wvdv2002/SMA-SB2500-Off-Grid/code/solarinv_CubeMX.png

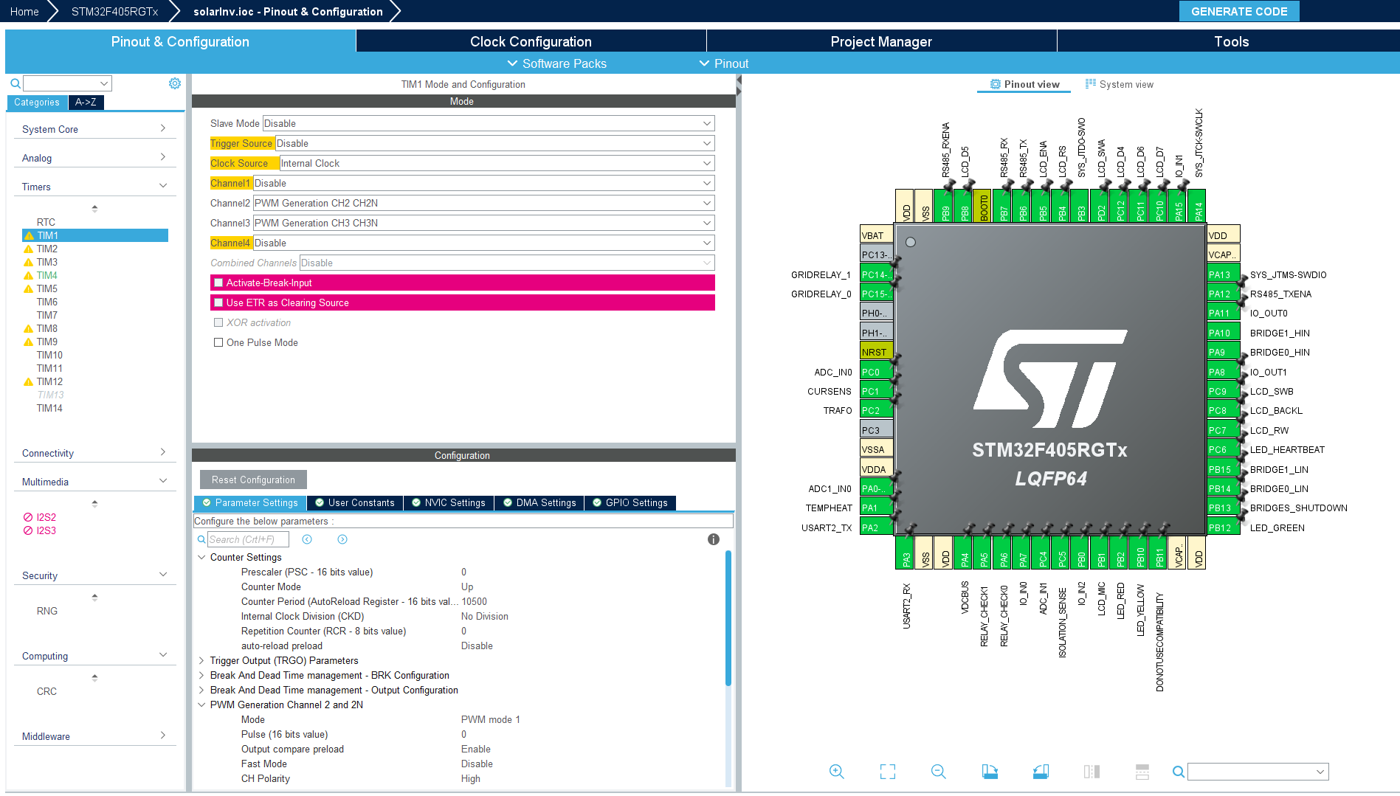
code/solarinv_CubeMX.png
