wvdv2002/SMA-SB2500-Off-Grid/images/2022-01-16 18.45.59.jpg

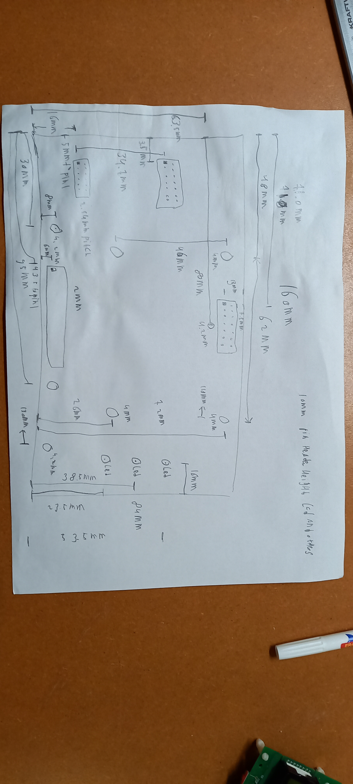
images/2022-01-16 18.45.59.jpg
