wvdv2002/SMA-SB2500-Off-Grid/images/commboardunderside.jpg

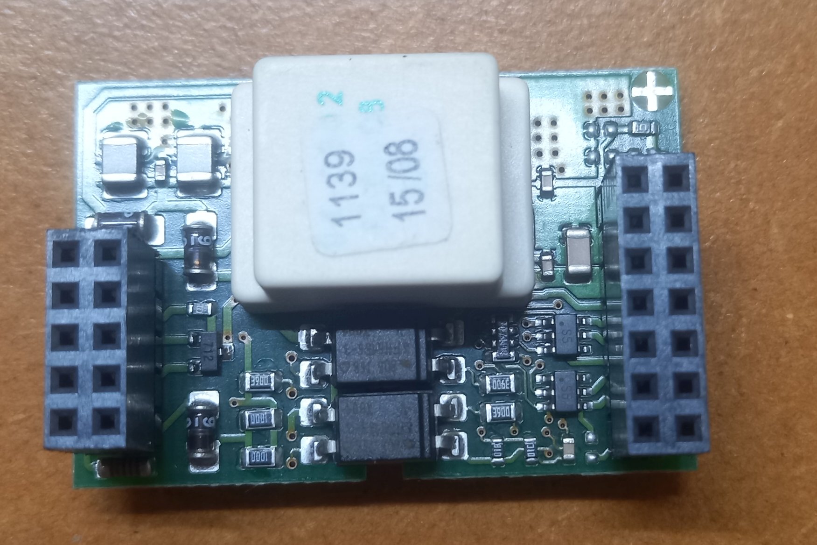
images/commboardunderside.jpg
