wvdv2002/SMA-SB2500-Off-Grid/images/DCBus.png

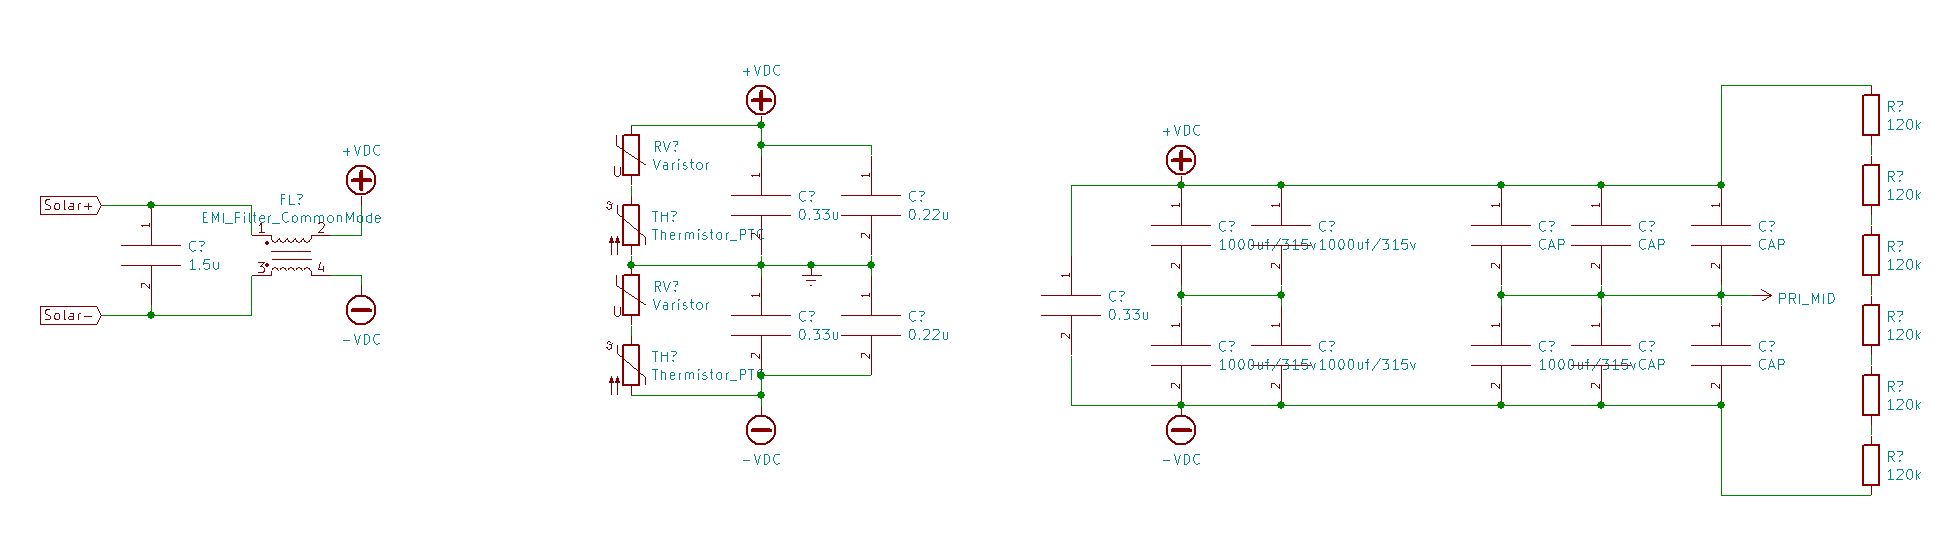
images/DCBus.png
