wvdv2002/SMA-SB2500-Off-Grid/images/EMCFilter.jpg

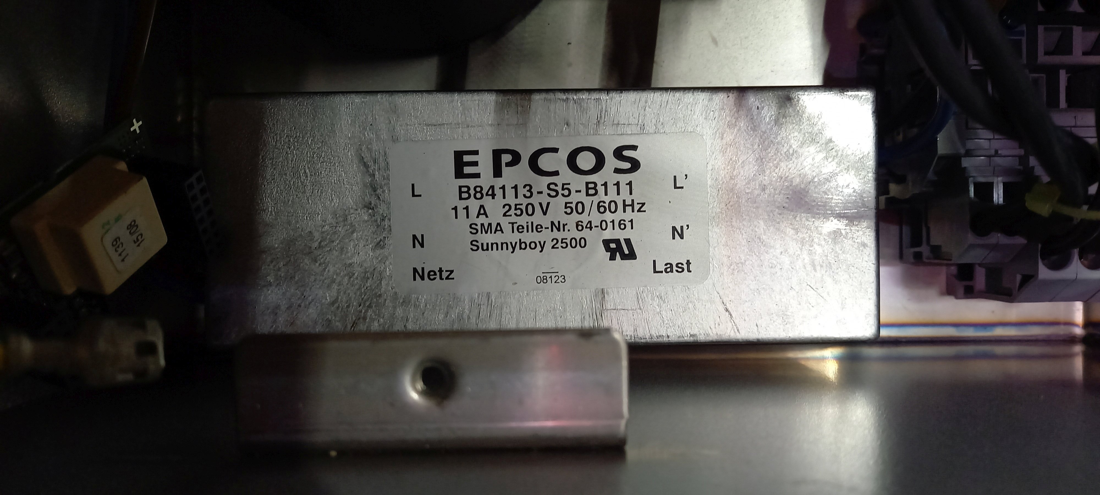
images/EMCFilter.jpg
