wvdv2002/SMA-SB2500-Off-Grid/images/inductor.jpg

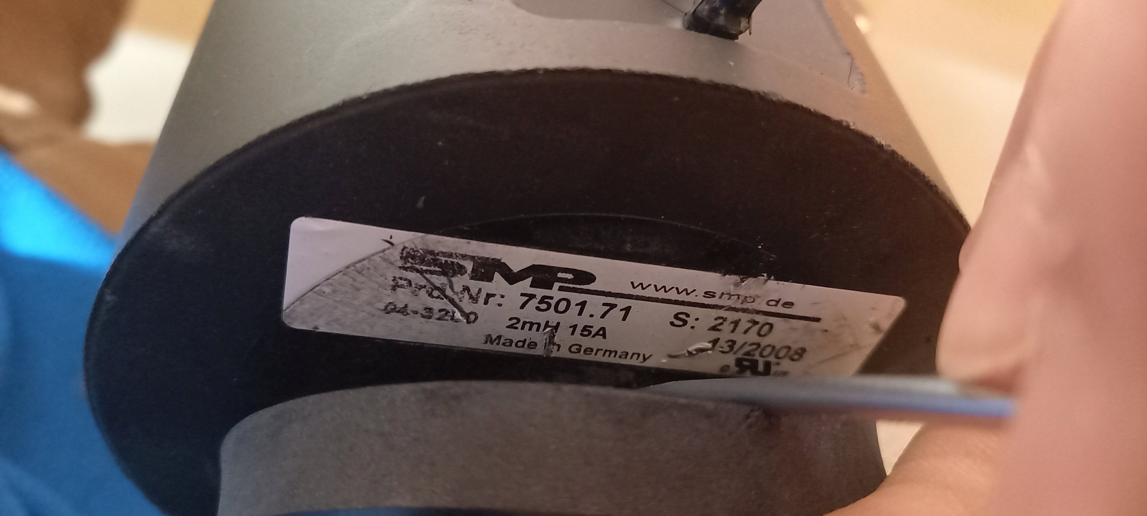
images/inductor.jpg
