wvdv2002/SMA-SB2500-Off-Grid/images/inverterInside.jpg

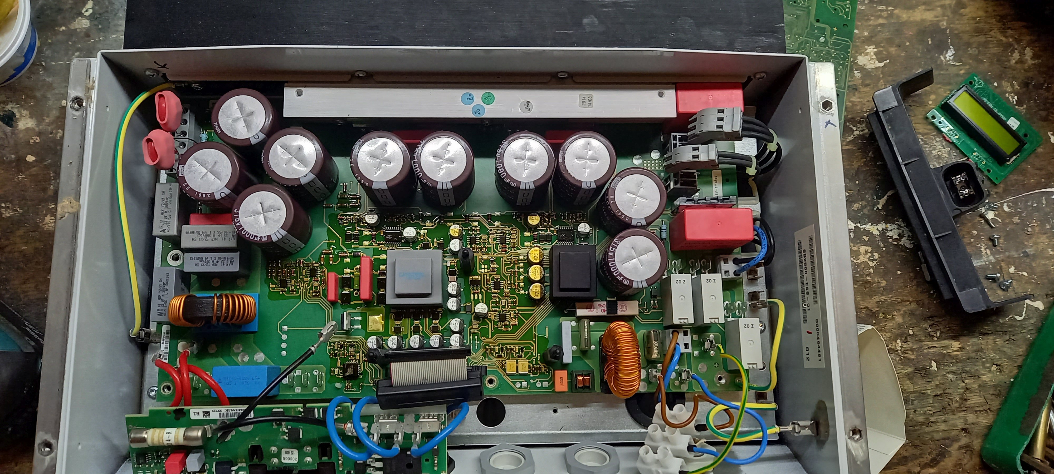
images/inverterInside.jpg
