wvdv2002/SMA-SB2500-Off-Grid/images/lcdon.jpg

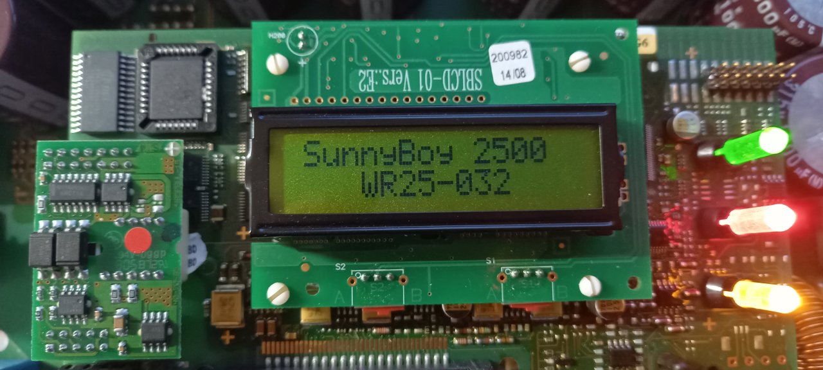
images/lcdon.jpg
