wvdv2002/SMA-SB2500-Off-Grid/images/logicboard2.jpg

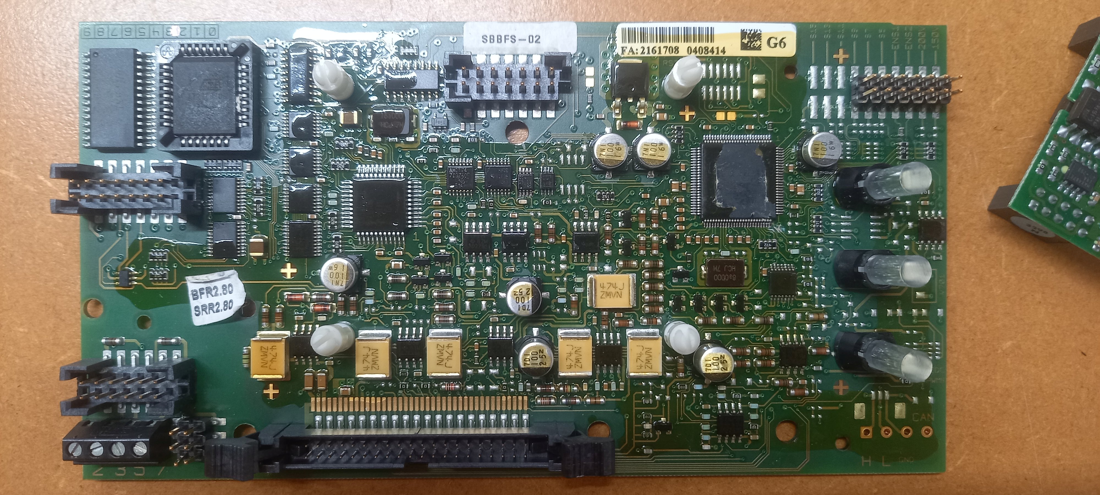
images/logicboard2.jpg
