wvdv2002/SMA-SB2500-Off-Grid/images/logicboard.jpg

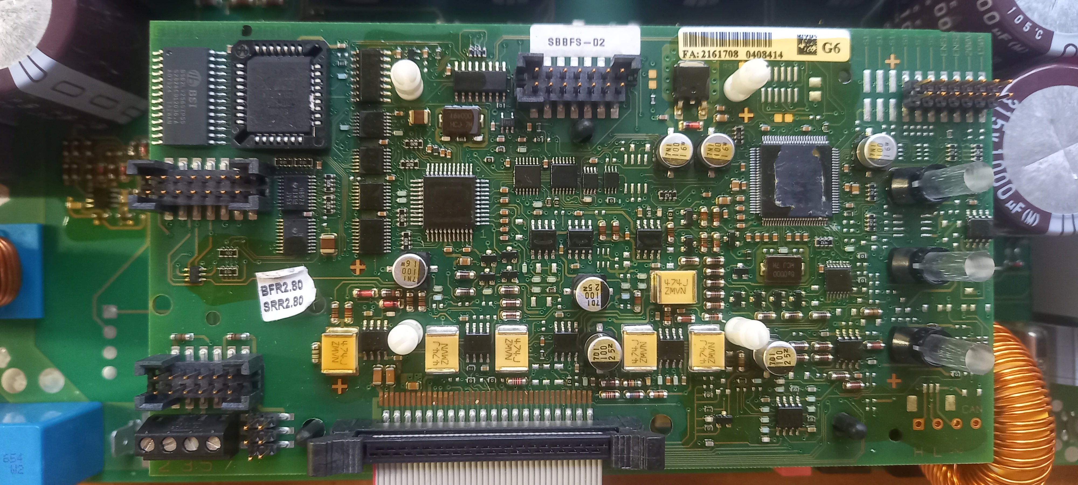
images/logicboard.jpg
