wvdv2002/SMA-SB2500-Off-Grid/images/logicboardcloseup.jpg

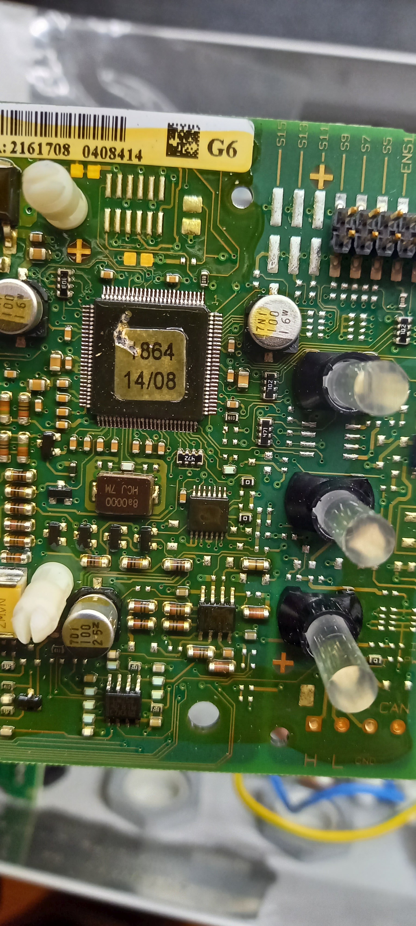
images/logicboardcloseup.jpg
