wvdv2002/SMA-SB2500-Off-Grid/images/logicboardcomplete.jpg

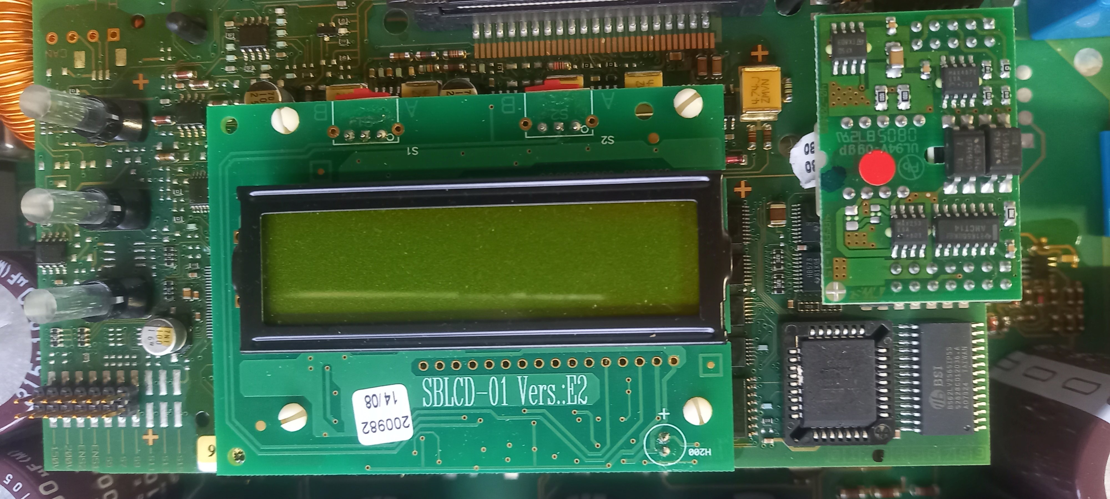
images/logicboardcomplete.jpg
