wvdv2002/SMA-SB2500-Off-Grid/images/LogicboardSizes.jpg

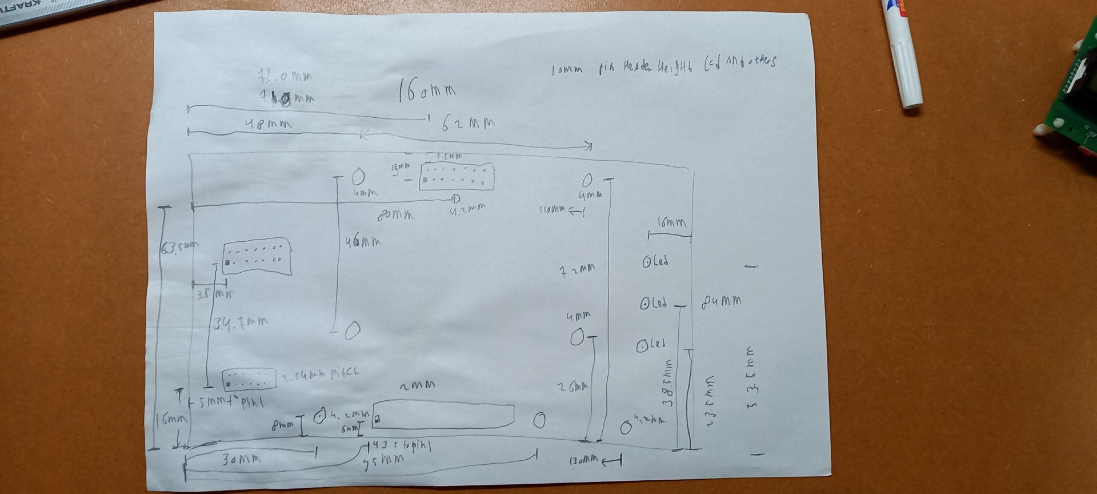
images/LogicboardSizes.jpg
