wvdv2002/SMA-SB2500-Off-Grid/images/logicboardunderside.jpg

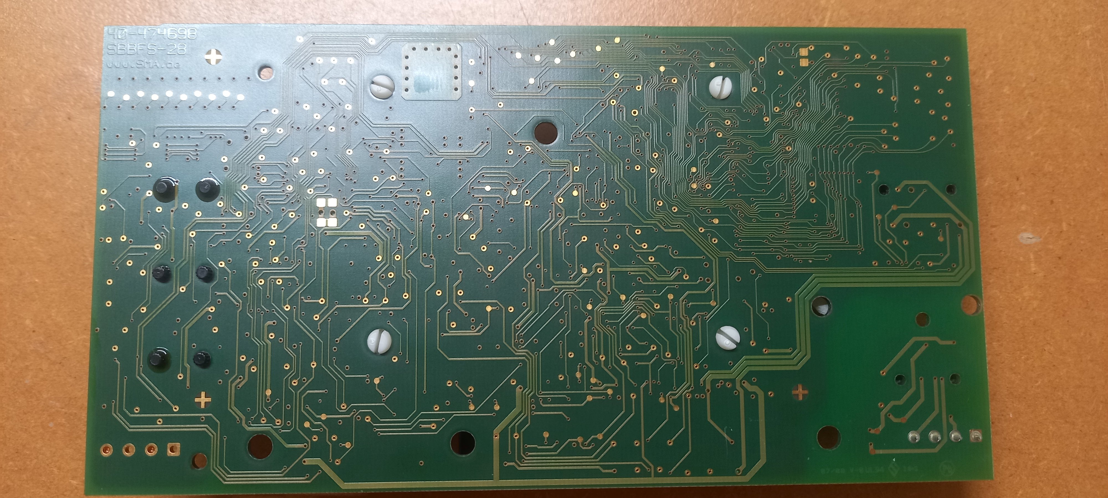
images/logicboardunderside.jpg
