wvdv2002/SMA-SB2500-Off-Grid/images/newController/controllerPCB.jpg

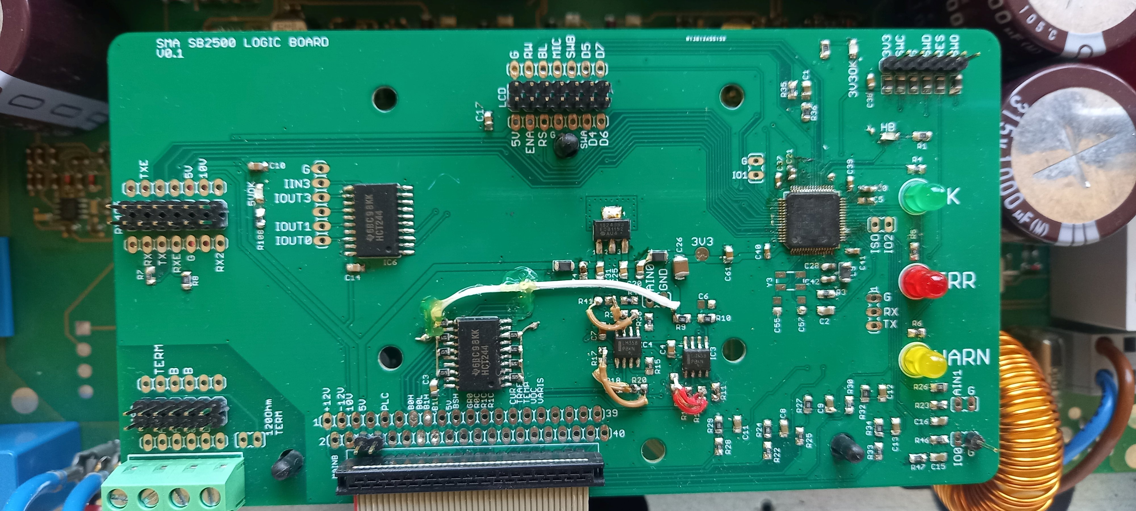
images/newController/controllerPCB.jpg
