wvdv2002/SMA-SB2500-Off-Grid/images/powerboard2.jpg

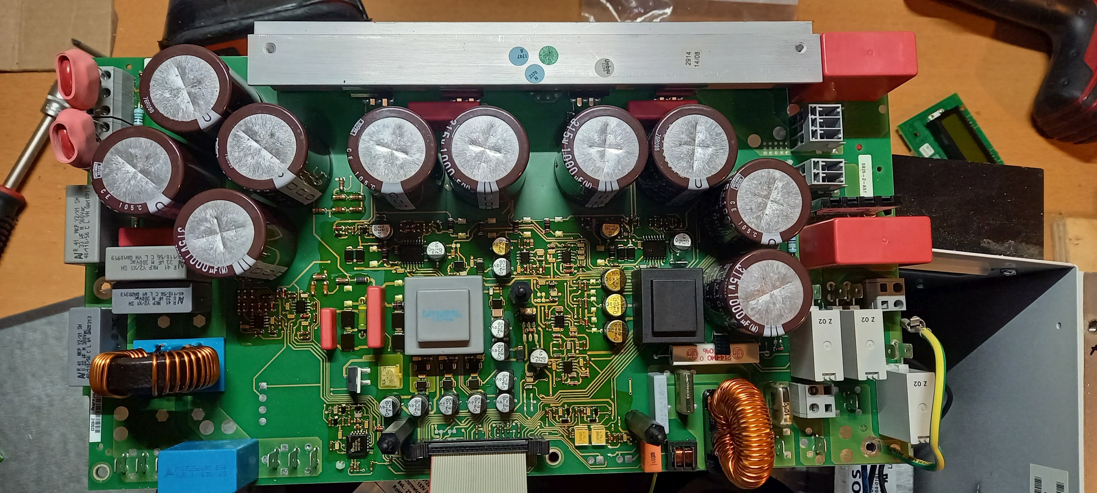
images/powerboard2.jpg
