wvdv2002/SMA-SB2500-Off-Grid/images/powerboardunderside.jpg

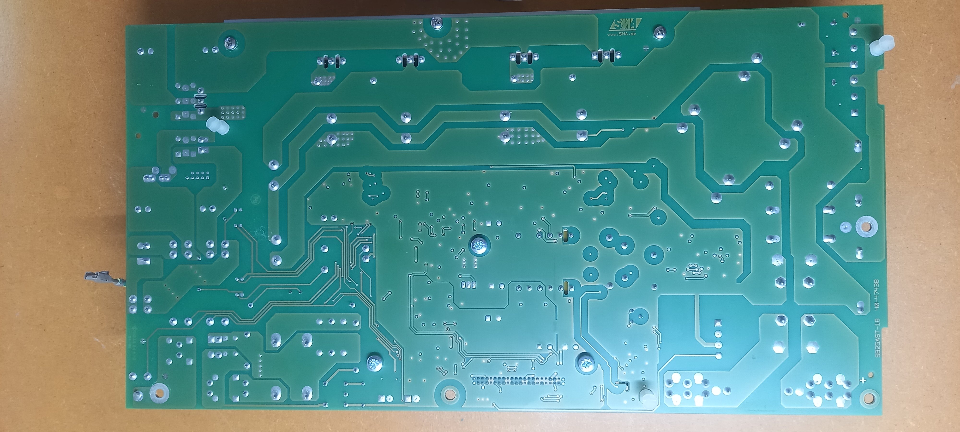
images/powerboardunderside.jpg
