wvdv2002/SMA-SB2500-Off-Grid/images/powerconnections.jpg

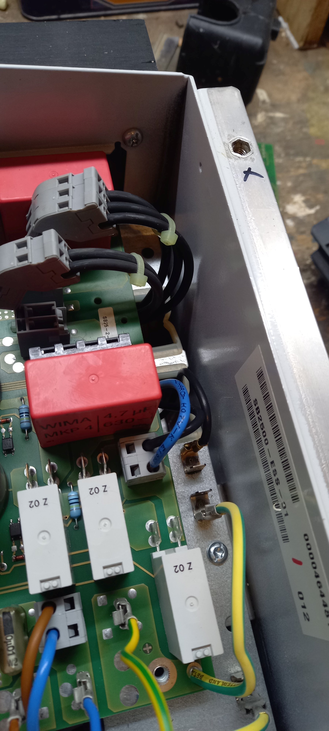
images/powerconnections.jpg
