wvdv2002/SMA-SB2500-Off-Grid/images/powertrain.png

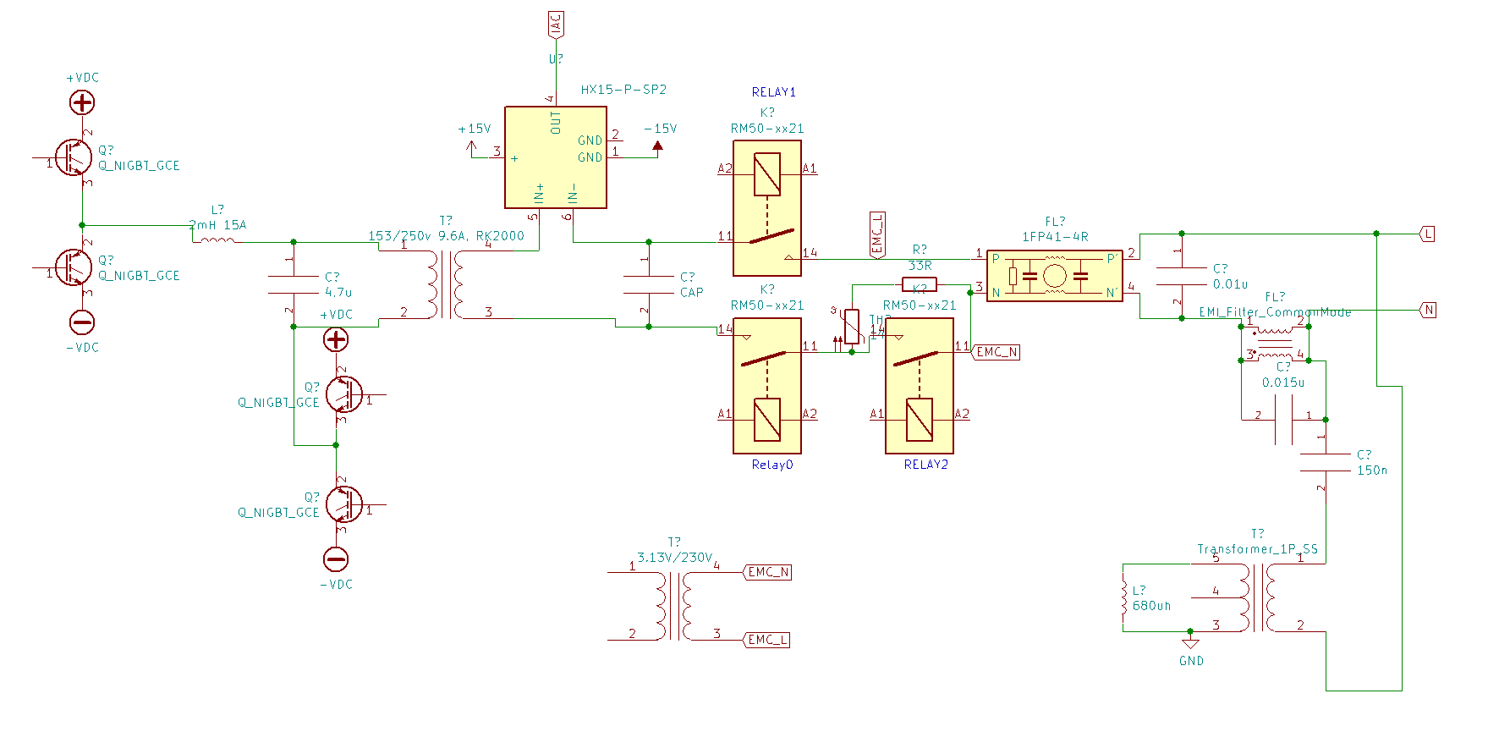
images/powertrain.png
