wvdv2002/SMA-SB2500-Off-Grid/images/SecondLayer.jpg

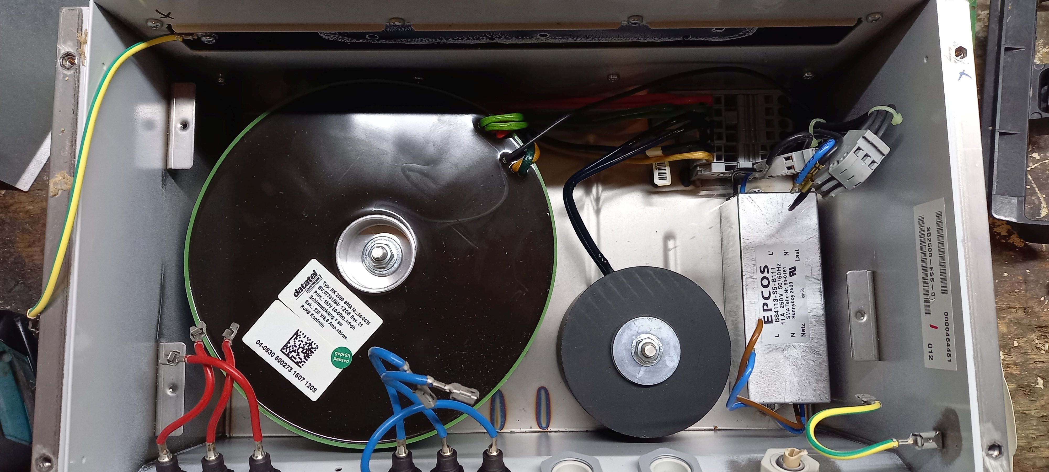
images/SecondLayer.jpg
