wvdv2002/SMA-SB2500-Off-Grid/images/SMPS.jpg

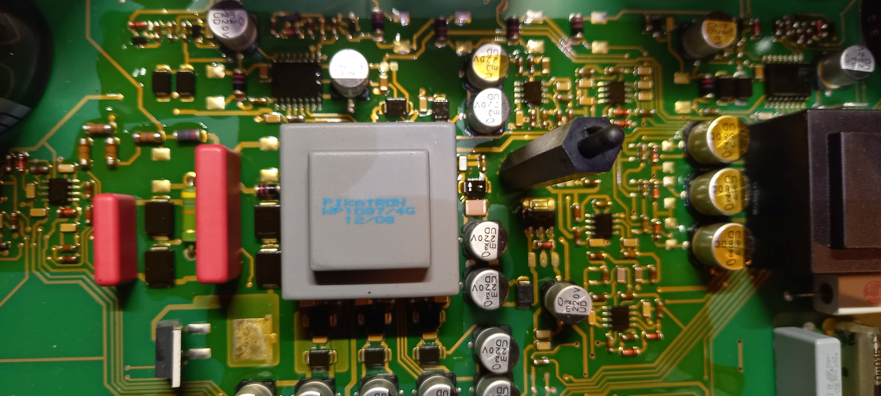
images/SMPS.jpg
