wvdv2002/SMA-SB2500-Off-Grid/images/terminalconnections.jpg

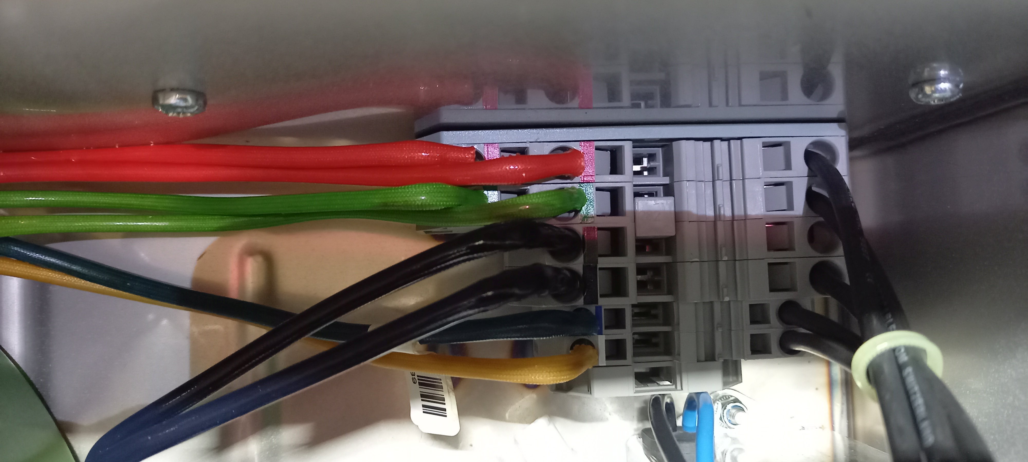
images/terminalconnections.jpg
