wvdv2002/SMA-SB2500-Off-Grid/images/Transformer.jpg

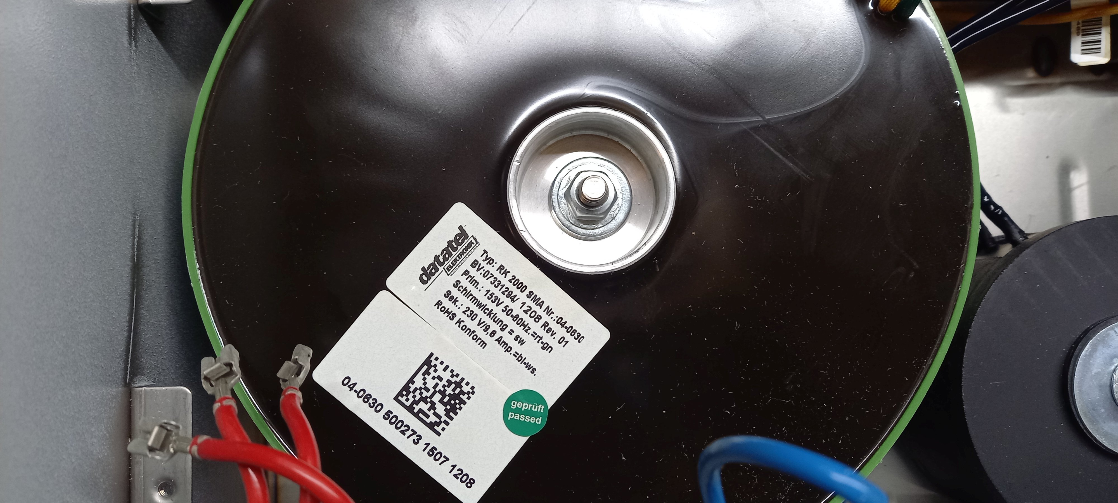
images/Transformer.jpg
