wvdv2002/SMA-SB2500-Off-Grid/PCB/logic_v01_back.png

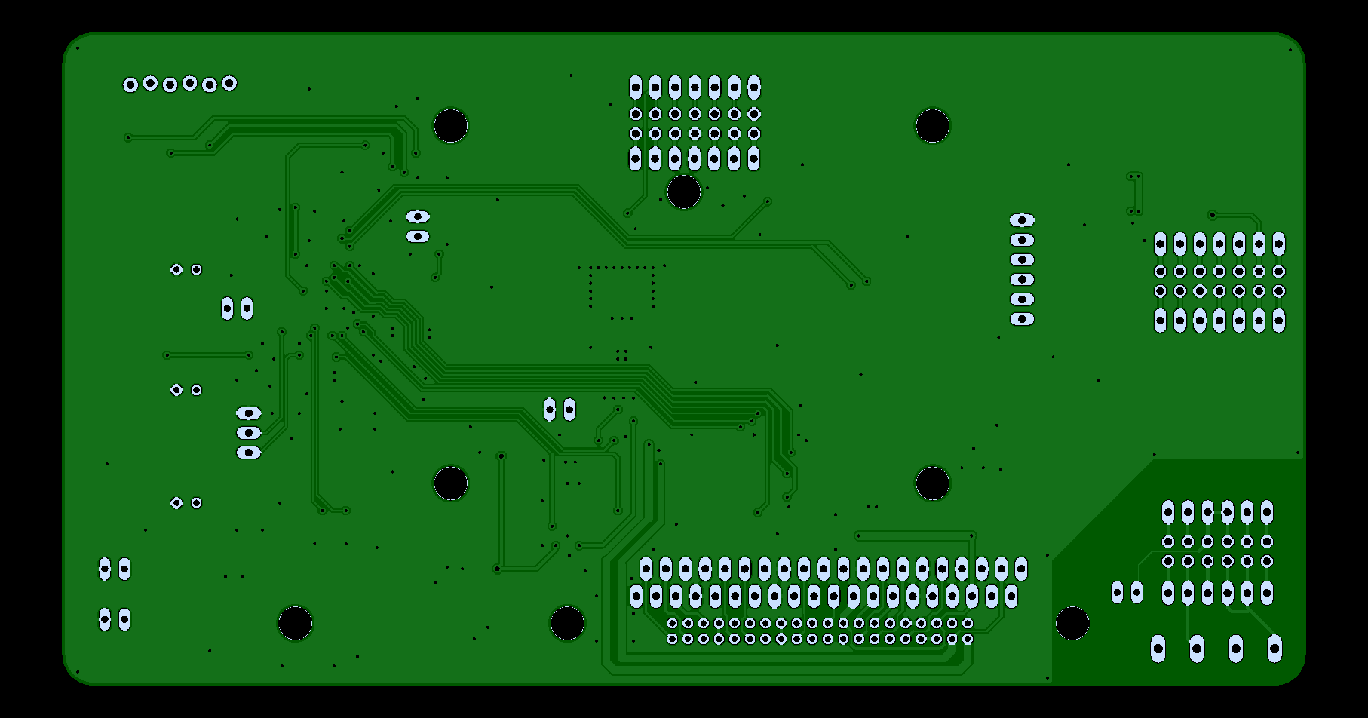
PCB/logic_v01_back.png
