wvdv2002/SMA-SB2500-Off-Grid/PCB/logic_v01_front.png

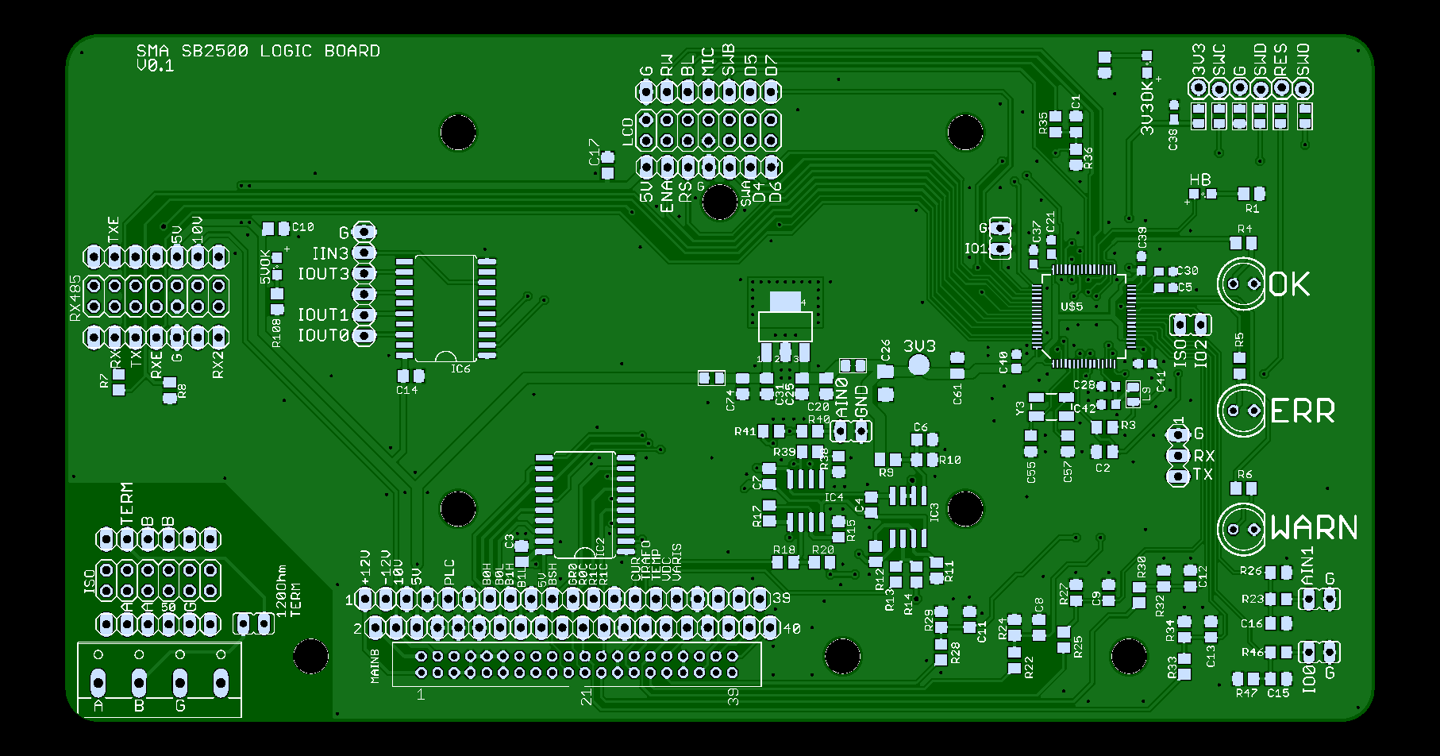
PCB/logic_v01_front.png
