wvdv2002/SMA-SB2500-Off-Grid/images/measurementtransfo.jpg

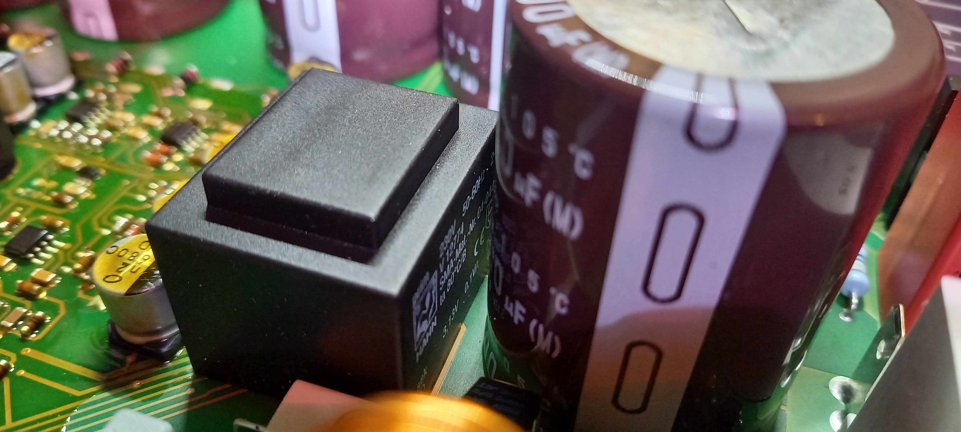
images/measurementtransfo.jpg
