wvdv2002/SMA-SB2500-Off-Grid/simulations/SB2500.asc

C1: cap; 4.7µ
C2: cap; 4.7µ
L1: ind2; 24mH; Rser=0.1
L2: ind2; 55mH; Rser=0.1
L3: ind; 2mH
R1: res; 10
S1: sw
S2: sw
S3: sw
S4: sw
V1: voltage; PULSE(1 -1 0 31.25u 31.25u 0 62.5u)
V2: voltage; 100
V3: voltage; SINE(0 1 50 0 0 90)
Named nets: 0, Vh, Vbus, Vl, Vtria, Vref, Vout, Vin
K1 L1 L2 0.95
.param VDC 5
.tran 0 1 0 5.1u uic
.model SW SW(Ron=.01 Roff=1Meg Vt=0 Vh=5m)
Turns ratio: 153/230=0.66
Inductance: 100mH and 43mH
.meas avg I(V2)*Vbus
