wvdv2002/SMA-SB2500-Off-Grid/code/solarInv/Inc/filterCoeff.h

/*
 * filterCoeff.h
 *
 *  Created on: 29 aug. 2017
 *      Author: wvdv2
 */

#ifndef FILTERCOEFF_H_
#define FILTERCOEFF_H_



/*
# Sampling frequency, Hz
sampling_f = 1250.0
# Cutoff frequency, Hz
cutoff_f = [100]
lowPass = True
*/
const int uCapFilterCoeffSize = 32;
float uCapFilterCoeffFloat[32] = {
    0.00163443435600736457734,
    0.00165206265187668320700,
    0.00132794487907094750125,
    -0.00000000000000000100998,
    -0.00296514230488699546268,
    -0.00756958558276418433386,
    -0.01267485250794285131515,
    -0.01588651227076341362898,
    -0.01400758055841758685511,
    -0.00400922275381298057195,
    0.01577041530778454381245,
    0.04463530715119806702162,
    0.07916865804280681651051,
    0.11373029919080657190733,
    0.14174874743108617503040,
    0.15744502696795084628612,
    0.15744502696795084628612,
    0.14174874743108617503040,
    0.11373029919080657190733,
    0.07916865804280681651051,
    0.04463530715119808089941,
    0.01577041530778454728190,
    -0.00400922275381298143931,
    -0.01400758055841758858984,
    -0.01588651227076342056788,
    -0.01267485250794285478459,
    -0.00756958558276418433386,
    -0.00296514230488699546268,
    -0.00000000000000000100998,
    0.00132794487907094750125,
    0.00165206265187668320700,
    0.00163443435600736457734,
};


const int currentFilterCoefSize = 201;
/*
# Sampling frequency, Hz
sampling_f = 1250.0
# Cutoff frequency, Hz
cutoff_f = [15.0]
lowPass = True
//# Number of taps/ coefficients for FIR filter. (Order + 1)
taps_n = 201
*/

float currentFilterCoef[201] = {
    0.00024168533744128116295,
    0.00023813171135975808685,
    0.00023441115503548124095,
    0.00023038991157978394022,
    0.00022589217475085329886,
    0.00022070166759828862158,
    0.00021456396679225774016,
    0.00020718956371545277362,
    0.00019825764431065839768,
    0.00018742056063568909570,
    0.00017430895818030078099,
    0.00015853751434561036372,
    0.00013971123517335354682,
    0.00011743224953530642272,
    0.00009130703264426211555,
    0.00006095398401444257150,
    0.00002601127896306796626,
    -0.00001385509251842097271,
    -0.00005894319011698708919,
    -0.00010950698488838236141,
    -0.00016574831496643250553,
    -0.00022780903354419944156,
    -0.00029576344792407185079,
    -0.00036961114792810265128,
    -0.00044927032039314212467,
    -0.00053457164384689589802,
    -0.00062525285378172204814,
    -0.00072095406423424313741,
    -0.00082121392567326438518,
    -0.00092546669253925695816,
    -0.00103304026621936712385,
    -0.00114315527084603144915,
    -0.00125492521014771546937,
    -0.00136735774373857466718,
    -0.00147935711079964218526,
    -0.00158972771817407943114,
    -0.00169717889857616240426,
    -0.00180033083300613992034,
    -0.00189772161968342284802,
    -0.00198781545997414729396,
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
};



#endif /* FILTERCOEFF_H_ */
