wvdv2002/SMA-SB2500-Off-Grid/code/solarInv/Src/flash_helper.c

/*
	Copyright 2012-2015 Benjamin Vedder	benjamin@vedder.se

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
    You should have received a copy of the GNU General Public License
    along with this program.  If not, see <http://www.gnu.org/licenses/>.
    */

/*
 * flash_helper.c
 *
 *  Created on: 6 maj 2015
 *      Author: benjamin
 */

#include "flash_helper.h"


/*
 * Defines
 */
#define FLASH_SECTORS			12
#define BOOTLOADER_BASE			11
#define APP_BASE				0
#define NEW_APP_BASE			8
#define NEW_APP_SECTORS			3

// Base address of the Flash sectors
#define ADDR_FLASH_SECTOR_0     ((uint32_t)0x08000000) // Base @ of Sector 0, 16 Kbytes
#define ADDR_FLASH_SECTOR_1     ((uint32_t)0x08004000) // Base @ of Sector 1, 16 Kbytes
#define ADDR_FLASH_SECTOR_2     ((uint32_t)0x08008000) // Base @ of Sector 2, 16 Kbytes
#define ADDR_FLASH_SECTOR_3     ((uint32_t)0x0800C000) // Base @ of Sector 3, 16 Kbytes
#define ADDR_FLASH_SECTOR_4     ((uint32_t)0x08010000) // Base @ of Sector 4, 64 Kbytes
#define ADDR_FLASH_SECTOR_5     ((uint32_t)0x08020000) // Base @ of Sector 5, 128 Kbytes
#define ADDR_FLASH_SECTOR_6     ((uint32_t)0x08040000) // Base @ of Sector 6, 128 Kbytes
#define ADDR_FLASH_SECTOR_7     ((uint32_t)0x08060000) // Base @ of Sector 7, 128 Kbytes
#define ADDR_FLASH_SECTOR_8     ((uint32_t)0x08080000) // Base @ of Sector 8, 128 Kbytes
#define ADDR_FLASH_SECTOR_9     ((uint32_t)0x080A0000) // Base @ of Sector 9, 128 Kbytes
#define ADDR_FLASH_SECTOR_10    ((uint32_t)0x080C0000) // Base @ of Sector 10, 128 Kbytes
#define ADDR_FLASH_SECTOR_11    ((uint32_t)0x080E0000) // Base @ of Sector 11, 128 Kbytes

// Private constants
static const uint32_t flash_addr[FLASH_SECTORS] = {
		ADDR_FLASH_SECTOR_0,
		ADDR_FLASH_SECTOR_1,
		ADDR_FLASH_SECTOR_2,
		ADDR_FLASH_SECTOR_3,
		ADDR_FLASH_SECTOR_4,
		ADDR_FLASH_SECTOR_5,
		ADDR_FLASH_SECTOR_6,
		ADDR_FLASH_SECTOR_7,
		ADDR_FLASH_SECTOR_8,
		ADDR_FLASH_SECTOR_9,
		ADDR_FLASH_SECTOR_10,
		ADDR_FLASH_SECTOR_11
};
static const uint8_t flash_sector[12] = {
		FLASH_SECTOR_0,
		FLASH_SECTOR_1,
		FLASH_SECTOR_2,
		FLASH_SECTOR_3,
		FLASH_SECTOR_4,
		FLASH_SECTOR_5,
		FLASH_SECTOR_6,
		FLASH_SECTOR_7,
		FLASH_SECTOR_8,
		FLASH_SECTOR_9,
		FLASH_SECTOR_10,
		FLASH_SECTOR_11
};

uint16_t flash_helper_erase_new_app(uint32_t new_app_size) {
	HAL_FLASH_Unlock();
	__HAL_FLASH_CLEAR_FLAG(FLASH_FLAG_OPERR | FLASH_FLAG_WRPERR | FLASH_FLAG_PGAERR |
			FLASH_FLAG_PGPERR | FLASH_FLAG_PGSERR);

	new_app_size += flash_addr[NEW_APP_BASE];

	//mc_interface_unlock();
	//mc_interface_release_motor();
	//utils_sys_lock_cnt();
	//RCC_APB1PeriphClockCmd(RCC_APB1Periph_WWDG, DISABLE);

	for (int i = 0;i < NEW_APP_SECTORS;i++) {
		if (new_app_size > flash_addr[NEW_APP_BASE + i]) {
			FLASH_Erase_Sector(flash_sector[NEW_APP_BASE + i], FLASH_VOLTAGE_RANGE_3);
		} else {
			break;
		}
	}

	//RCC_APB1PeriphClockCmd(RCC_APB1Periph_WWDG, ENABLE);
	//utils_sys_unlock_cnt();

	return HAL_OK;
}

uint16_t flash_helper_write_new_app_data(uint32_t offset, uint8_t *data, uint32_t len) {
	__HAL_FLASH_CLEAR_FLAG(FLASH_FLAG_OPERR | FLASH_FLAG_WRPERR | FLASH_FLAG_PGAERR |
			FLASH_FLAG_PGPERR | FLASH_FLAG_PGSERR);

	//mc_interface_unlock();
	//mc_interface_release_motor();
	//utils_sys_lock_cnt();
	//RCC_APB1PeriphClockCmd(RCC_APB1Periph_WWDG, DISABLE);

	for (uint32_t i = 0;i < len;i++) {
		uint16_t res = HAL_FLASH_Program(FLASH_TYPEPROGRAM_BYTE,flash_addr[NEW_APP_BASE] + offset + i, data[i]);
//		uint16_t res = HAL_OK;
		if (res != HAL_OK) {
			return res;
		}
	}

//	RCC_APB1PeriphClockCmd(RCC_APB1Periph_WWDG, ENABLE);
//	utils_sys_unlock_cnt();

	return HAL_OK;
}

/**
 * Stop the system and jump to the bootloader.
 */
void flash_helper_jump_to_bootloader(void) {
	typedef void (*pFunction)(void);

	//mc_interface_unlock();
	//mc_interface_release_motor();
	//usbDisconnectBus(&USBD1);
	//usbStop(&USBD1);

	//uartStop(&HW_UART_DEV);
	//palSetPadMode(HW_UART_TX_PORT, HW_UART_TX_PIN, PAL_MODE_INPUT);
	//palSetPadMode(HW_UART_RX_PORT, HW_UART_RX_PIN, PAL_MODE_INPUT);

	// Disable watchdog
	//RCC_APB1PeriphClockCmd(RCC_APB1Periph_WWDG, DISABLE);

	//chSysDisable();
	vTaskSuspendAll();
	HAL_RCC_DeInit();
	HAL_DeInit();


	pFunction jump_to_bootloader;

	// Variable that will be loaded with the start address of the application
	volatile uint32_t* jump_address;
	const volatile uint32_t* bootloader_address = (volatile uint32_t*)0x080E0000;

	// Get jump address from application vector table
	jump_address = (volatile uint32_t*) bootloader_address[1];

	// Load this address into function pointer
	jump_to_bootloader = (pFunction) jump_address;

	// Clear pending interrupts
	SCB->ICSR = SCB_ICSR_PENDSVCLR_Msk;

	// Disable all interrupts
	for(int i = 0;i < 8;i++) {
		NVIC->ICER[i] = NVIC->IABR[i];
	}

	// Set stack pointer
	__set_MSP((uint32_t) (bootloader_address[0]));

	// Jump to the bootloader
	jump_to_bootloader();
}

uint8_t* flash_helper_get_sector_address(uint32_t fsector) {
	uint8_t *res = 0;

	for (int i = 0;i < FLASH_SECTORS;i++) {
		if (flash_sector[i] == fsector) {
			res = (uint8_t *)flash_addr[i];
			break;
		}
	}

	return res;
}
